Mondrol/InkTime_SmartWatch/Images/Screenshot 2026-04-19 184929.png

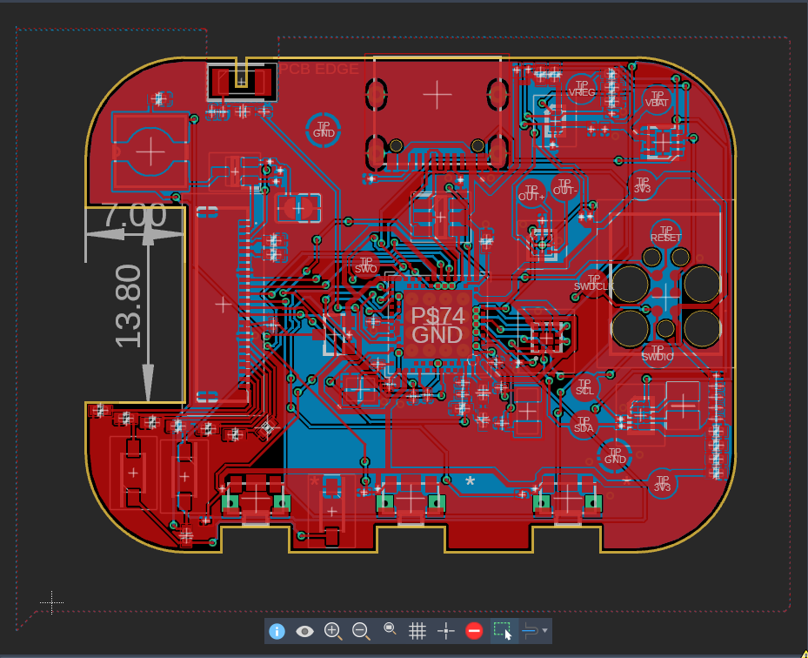
Images/Screenshot 2026-04-19 184929.png
