Mondrol/InkTime_SmartWatch/Images/Screenshot 2026-04-19 185629.png

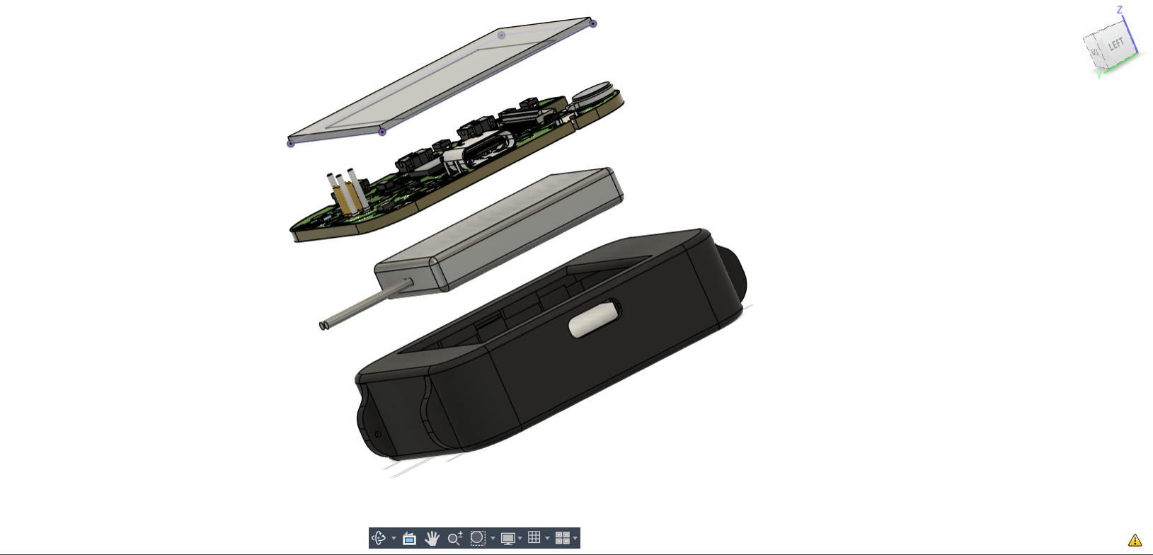
Images/Screenshot 2026-04-19 185629.png
